ohguma/mega_board/documents/pcb202210a.png

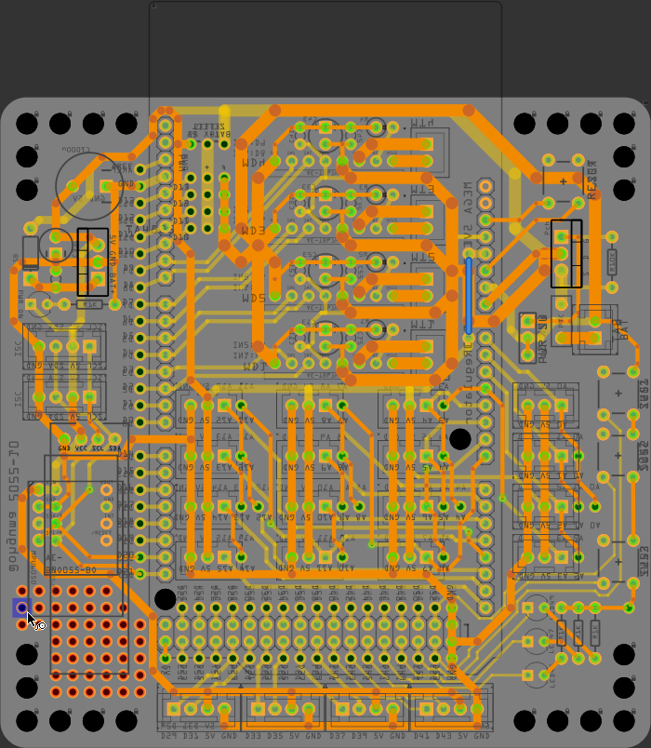
documents/pcb202210a.png
