ohguma/mega_board/documents/pcb202210b.png

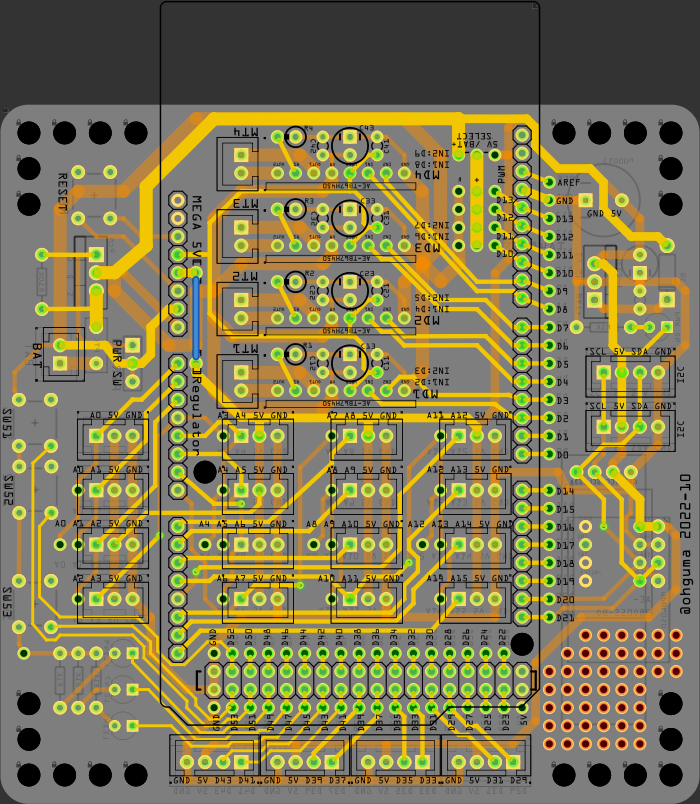
documents/pcb202210b.png
